sy2002/DM65PIC/00-STM32F429_LIBRARIES/tm_stm32f4_adc.h

/**
 * @author  Tilen Majerle
 * @email   tilen@majerle.eu
 * @website http://stm32f4-discovery.com
 * @link    http://stm32f4-discovery.com/2014/04/library-06-ad-converter-on-stm32f4xx/
 * @version v1.2
 * @ide     Keil uVision
 * @license GNU GPL v3
 * @brief   ADC library for STM32F4xx
 *	
@verbatim
   ----------------------------------------------------------------------
    Copyright (C) Tilen Majerle, 2015
    
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
    You should have received a copy of the GNU General Public License
    along with this program.  If not, see <http://www.gnu.org/licenses/>.
   ----------------------------------------------------------------------
@endverbatim
 */
#ifndef TM_ADC_H
#define TM_ADC_H 120

/**
 * @addtogroup TM_STM32F4xx_Libraries
 * @{
 */

/**
 * @defgroup TM_ADC
 * @brief    ADC library for STM32F4xx - http://stm32f4-discovery.com/2014/04/library-06-ad-converter-on-stm32f4xx/
 * @{
 *
 * This library allows you to operate with ADC peripheral on STM32F4xx devices.
 *
 * \par ADC pinout
 *
@verbatim
CHANNEL   ADC1   ADC2   ADC3

0         PA0    PA0    PA0
1         PA1    PA1    PA1
2         PA2    PA2    PA2
3         PA3    PA3    PA3
4         PA4    PA4    PF6
5         PA5    PA5    PF7
6         PA6    PA6    PF8
7         PA7    PA7    PF9
8         PB0    PB0    PF10
9         PB1    PB1    PF3
10        PC0    PC0    PC0
11        PC1    PC1    PC1
12        PC2    PC2    PC2
13        PC3    PC3    PC3
14        PC4    PC4    PF4
15        PC5    PC5    PF5
@endverbatim
 *
 * \par Changelog
 *
@verbatim
 Version 1.2
  - March 08, 2015
  - Support for new GPIO system

 Version 1.1
  - November 02, 2014
  - Added support for measure Vbat pin with ADC

 Version 1.0
  - First release
@endverbatim
 *
 * \par Dependencies
 *
@verbatim
 - STM32F4xx
 - STM32F4xx RCC
 - STM32F4xx GPIO
 - STM32F4xx ADC
 - defines.h
 - TM GPIO
@endverbatim
 */
#include "stm32f4xx.h"
#include "stm32f4xx_rcc.h"
#include "stm32f4xx_gpio.h"
#include "stm32f4xx_adc.h"
#include "defines.h"
#include "tm_stm32f4_gpio.h"

/**
 * @defgroup TM_ADC_Macros
 * @brief    Library defines
 * @{
 */

/**
 * @brief  Default resolution for ADC1
 */
#ifndef TM_ADC1_RESOLUTION
#define TM_ADC1_RESOLUTION		ADC_Resolution_12b
#endif

/**
 * @brief  Default resolution for ADC2
 */
#ifndef TM_ADC2_RESOLUTION
#define TM_ADC2_RESOLUTION		ADC_Resolution_12b
#endif

/**
 * @brief  Default resolution for ADC3
 */
#ifndef TM_ADC3_RESOLUTION
#define TM_ADC3_RESOLUTION		ADC_Resolution_12b
#endif

/**
 * @brief  Default supply voltage in mV
 */
#ifndef ADC_SUPPLY_VOLTAGE
#define ADC_SUPPLY_VOLTAGE		3300
#endif

/**
 * @brief  Multipliers for VBAT measurement */
#if defined (STM32F40_41xxx)
#define ADC_VBAT_MULTI			2
#endif
#if defined (STM32F427_437xx) || defined (STM32F429_439xx) || defined (STM32F401xx) || defined (STM32F411xE)
#define ADC_VBAT_MULTI			4
#endif

/**
 * @}
 */
 
/**
 * @defgroup TM_ADC_Typedefs
 * @brief    Library Typedefs
 * @{
 */

/**
 * @brief  ADC available channels
 */
typedef enum {
	TM_ADC_Channel_0,  /*!< Operate with ADC channel 0 */
	TM_ADC_Channel_1,  /*!< Operate with ADC channel 1 */
	TM_ADC_Channel_2,  /*!< Operate with ADC channel 2 */
	TM_ADC_Channel_3,  /*!< Operate with ADC channel 3 */
	TM_ADC_Channel_4,  /*!< Operate with ADC channel 4 */
	TM_ADC_Channel_5,  /*!< Operate with ADC channel 5 */
	TM_ADC_Channel_6,  /*!< Operate with ADC channel 6 */
	TM_ADC_Channel_7,  /*!< Operate with ADC channel 7 */
	TM_ADC_Channel_8,  /*!< Operate with ADC channel 8 */
	TM_ADC_Channel_9,  /*!< Operate with ADC channel 9 */
	TM_ADC_Channel_10, /*!< Operate with ADC channel 10 */
	TM_ADC_Channel_11, /*!< Operate with ADC channel 11 */
	TM_ADC_Channel_12, /*!< Operate with ADC channel 12 */
	TM_ADC_Channel_13, /*!< Operate with ADC channel 13 */
	TM_ADC_Channel_14, /*!< Operate with ADC channel 14 */
	TM_ADC_Channel_15, /*!< Operate with ADC channel 15 */
	TM_ADC_Channel_16, /*!< Operate with ADC channel 16 */
	TM_ADC_Channel_17, /*!< Operate with ADC channel 17 */
	TM_ADC_Channel_18  /*!< Operate with ADC channel 18 */
} TM_ADC_Channel_t;

/**
 * @}
 */

/**
 * @defgroup TM_ADC_Functions
 * @brief    Library Functions
 * @{
 */

/**
 * @brief  Initializes ADCx peripheral
 * @param  *ADCx: ADCx peripheral to initialize
 * @retval None
 */
void TM_ADC_InitADC(ADC_TypeDef* ADCx);

/**
 * @brief  Initializes ADCx with ADCx channel
 * @param  *ADCx: ADCx peripheral to operate with
 * @param  channel: channel for ADCx
 * @retval None
 */
void TM_ADC_Init(ADC_TypeDef* ADCx, uint8_t channel);

/**
 * @brief  Reads from ADCx channel
 * @param  *ADCx: ADCx peripheral to operate with
 * @param  channel: channel for ADCx to read from
 * @retval ADC value
 */
uint16_t TM_ADC_Read(ADC_TypeDef* ADCx, uint8_t channel);

/**
 * @brief  Enables Vbat channel for ADC
 * @param  None
 * @retval None
 */
void TM_ADC_EnableVbat(void);

/**
 * @brief  Disables Vbat channel for ADC
 * @param  None
 * @retval None
 */
void TM_ADC_DisableVbat(void);

/**
 * @brief  Reads vbat pin voltage
 * @param  *ADCx: ADCx peripheral to use for Vbat measurement
 * @retval voltage in mV
 */
uint16_t TM_ADC_ReadVbat(ADC_TypeDef* ADCx);

/**
 * @}
 */
 
/**
 * @}
 */
 
/**
 * @}
 */

#endif
